Nikicoraz/SvegliaESP8266/include/html_index.h

#pragma once

const uint16_t html_index_L = 302;
const uint8_t html_index[] PROGMEM = {
	0x1f, 0x8b, 0x08, 0x00, 0x00, 0x00, 0x00, 0x00, 0x00, 0x03, 0x6d, 0x8f, 0xcd, 0x6e, 0x83, 0x30, 
	0x10, 0x84, 0xef, 0x79, 0x0a, 0x37, 0xe7, 0x52, 0x92, 0x5b, 0x45, 0x6c, 0x2e, 0xf9, 0x91, 0x7a, 
	0x6a, 0x24, 0x52, 0x55, 0x3d, 0x3a, 0xf6, 0x02, 0x2b, 0x19, 0xdb, 0xc2, 0x0b, 0x04, 0x55, 0x7d, 
	0xf7, 0x3a, 0x80, 0x2a, 0x55, 0xad, 0x0f, 0xb6, 0x76, 0x3c, 0xdf, 0xee, 0x0e, 0x7f, 0x38, 0xbc, 
	0xee, 0x2f, 0x1f, 0xe7, 0x23, 0xab, 0xa9, 0x31, 0x39, 0xbf, 0xdf, 0xcc, 0x48, 0x5b, 0x09, 0xb0, 
	0x39, 0x6f, 0x80, 0x24, 0x53, 0xb5, 0x6c, 0x03, 0x90, 0x78, 0xbb, 0x9c, 0x92, 0xe7, 0x45, 0xb3, 
	0xb2, 0x01, 0xd1, 0x23, 0x0c, 0xde, 0xb5, 0xc4, 0x94, 0xb3, 0x04, 0x96, 0xc4, 0x7a, 0x40, 0x4d, 
	0xb5, 0xd0, 0xd0, 0xa3, 0x82, 0x64, 0x2a, 0x1e, 0x19, 0x5a, 0x24, 0x94, 0x26, 0x09, 0x4a, 0x1a, 
	0x10, 0xdb, 0xa7, 0xcd, 0x3a, 0xe7, 0x84, 0x64, 0x20, 0x3f, 0x16, 0xe7, 0xa2, 0x87, 0xca, 0xa0, 
	0xe4, 0xe9, 0xac, 0xf0, 0x40, 0x63, 0x7c, 0x4a, 0xd7, 0x36, 0x9f, 0xa5, 0x81, 0x5b, 0xa2, 0xb1, 
	0x05, 0x45, 0xe8, 0x6c, 0xa6, 0x9c, 0xe9, 0x1a, 0xbb, 0x93, 0x06, 0x2b, 0x9b, 0x20, 0x41, 0x13, 
	0x32, 0x15, 0x67, 0x42, 0xbb, 0xab, 0xa4, 0xcf, 0xb6, 0x1b, 0x7f, 0xdb, 0x69, 0x0c, 0xde, 0xc8, 
	0x31, 0xbb, 0x93, 0x5f, 0x3c, 0x9d, 0x7b, 0xf1, 0xab, 0xd3, 0x63, 0xbe, 0x62, 0xf1, 0xf0, 0x7b, 
	0x5f, 0x26, 0xa7, 0x7e, 0x22, 0x8d, 0x91, 0xde, 0xb1, 0x44, 0x16, 0xf3, 0xd4, 0x4e, 0x0b, 0xef, 
	0x02, 0xcd, 0xb1, 0x86, 0xa8, 0x9e, 0xa2, 0x73, 0x86, 0x26, 0x10, 0xad, 0xef, 0x96, 0xdf, 0x10, 
	0x50, 0xb3, 0x38, 0x46, 0x41, 0xed, 0x8c, 0x86, 0x56, 0x14, 0xc5, 0xcb, 0xe1, 0x8f, 0x95, 0x46, 
	0x0f, 0xc2, 0xcb, 0x10, 0x06, 0xd7, 0xea, 0x19, 0x9c, 0xaa, 0xdf, 0xe8, 0x79, 0x31, 0xfc, 0x8f, 
	0x87, 0xee, 0xda, 0x20, 0xb1, 0x5e, 0x9a, 0x0e, 0xc4, 0xde, 0x59, 0x0b, 0x44, 0xb8, 0x24, 0x49, 
	0xcb, 0x9f, 0x05, 0x57, 0xab, 0x6f, 0xe3, 0x2e, 0x1a, 0xaf, 0xc4, 0x01, 0x00, 0x00 
};
